cvonk/OPNpool_meets_ESPHome/components/opnpool/opnpoolstate_rx.cpp

/**
 * @brief OPNpool - Pool state: updates the state in response to network messages
 *
 * © Copyright 2014, 2019, 2022, 2026, Coert Vonk
 * 
 * This file is part of OPNpool.
 * OPNpool is free software: you can redistribute it and/or modify it under the terms of
 * the GNU General Public License as published by the Free Software Foundation, either
 * version 3 of the License, or (at your option) any later version.
 * OPNpool is distributed in the hope that it will be useful, but WITHOUT ANY WARRANTY;
 * without even the implied warranty of MERCHANTABILITY or FITNESS FOR A PARTICULAR PURPOSE.
 * See the GNU General Public License for more details.
 * You should have received a copy of the GNU General Public License along with OPNpool. 
 * If not, see <https://www.gnu.org/licenses/>.
 * 
 * SPDX-License-Identifier: GPL-3.0-or-later
 * SPDX-FileCopyrightText: Copyright 2014,2019,2022,2026 Coert Vonk
 */

#include <string.h>
#include <esp_system.h>
#include <freertos/FreeRTOS.h>
#include <freertos/task.h>
#include <freertos/semphr.h>
#include <esphome/core/log.h>
#include <cJSON.h>

#include "utils.h"
#include "network.h"
#include "network_msg.h"
#include "ipc.h"
#include "opnpoolstate.h"
#include "opnpool.h"

namespace esphome {
namespace opnpool {

static char const * const TAG = "opnpoolstate_rx";

/**
 * ctrl
 **/

void
OpnPoolState::rx_ctrl_time(cJSON * const dbg, network_msg_ctrl_time_t const * const msg, poolstate_t * const state)
{
    state->system.tod.time.minute = msg->minute;
    state->system.tod.time.hour = msg->hour;
    state->system.tod.date.day = msg->day;
    state->system.tod.date.month = msg->month;
    state->system.tod.date.year = (uint16_t)(2000) + msg->year;

    if (ESPHOME_LOG_LEVEL >= ESPHOME_LOG_LEVEL_VERBOSE) {
        opnpoolstate_log_add_tod(dbg, "tod", &state->system.tod);
    }
}

void
OpnPoolState::rx_ctrl_heat_resp(cJSON * const dbg, network_msg_ctrl_heat_resp_t const * const msg, poolstate_t * const state)
{
    uint8_t const pool_idx = static_cast<uint8_t>(poolstate_thermo_typ_t::POOL);
    uint8_t const spa_idx = static_cast<uint8_t>(poolstate_thermo_typ_t::SPA);

    state->thermos[pool_idx].temp = msg->poolTemp;
    state->thermos[pool_idx].set_point = msg->poolSetpoint;
    state->thermos[pool_idx].heat_src = msg->heatSrc & 0x03;
    state->thermos[spa_idx].temp = msg->spaTemp;
    state->thermos[spa_idx].set_point = msg->spaSetpoint;
    state->thermos[spa_idx].heat_src = (msg->heatSrc >> 2) & 0x03;

    if (ESPHOME_LOG_LEVEL >= ESPHOME_LOG_LEVEL_VERBOSE) {
        opnpoolstate_log_add_thermos(dbg, "thermos", state->thermos, true, true, true, false);
    }
}

void
OpnPoolState::rx_ctrl_heat_set(cJSON * const dbg, network_msg_ctrl_heat_set_t const * const msg, poolstate_t * const state)
{
    uint8_t const pool_idx = static_cast<uint8_t>(poolstate_thermo_typ_t::POOL);
    uint8_t const spa_idx = static_cast<uint8_t>(poolstate_thermo_typ_t::SPA);

    state->thermos[pool_idx].set_point = msg->poolSetpoint;
    state->thermos[pool_idx].heat_src = msg->heatSrc & 0x03;
    state->thermos[spa_idx].set_point = msg->spaSetpoint;
    state->thermos[spa_idx].heat_src = (msg->heatSrc >> 2) & 0x03;

    if (ESPHOME_LOG_LEVEL >= ESPHOME_LOG_LEVEL_VERBOSE) {
        opnpoolstate_log_add_thermos(dbg, "thermos", state->thermos, false, true, true, false);
    }
}

static void
_rx_ctrl_hex_bytes(cJSON * const dbg, uint8_t const * const bytes, poolstate_t * const state, uint8_t nrBytes)
{
    if (ESPHOME_LOG_LEVEL >= ESPHOME_LOG_LEVEL_VERBOSE) {
        cJSON * const array = cJSON_CreateArray();
        
        for (uint_least8_t ii = 0; ii < nrBytes; ii++) {
            char hex_str[3];  // "XX\0"
            ESP_LOGVV(TAG, "byte[%u] = 0x%02X", ii, bytes[ii]);
            snprintf(hex_str, sizeof(hex_str), "%02X", bytes[ii]);
            cJSON_AddItemToArray(array, cJSON_CreateString(hex_str));
        }
        cJSON_AddItemToObject(dbg, "raw", array);
    }
}

void
OpnPoolState::rx_ctrl_circuit_set(cJSON * const dbg, network_msg_ctrl_circuit_set_t const * const msg, poolstate_t * const state)
{
    state->circuits.active[msg->circuit -1] = msg->value;

    if (ESPHOME_LOG_LEVEL >= ESPHOME_LOG_LEVEL_VERBOSE) {
        {
            int idx = static_cast<int>(msg->circuit) - 1;
            if (idx >= 0) {
                cJSON_AddNumberToObject(dbg, network_pool_circuit_str(static_cast<network_pool_circuit_t>(idx)), msg->value);
            } else {
                cJSON_AddNumberToObject(dbg, "circuit_invalid", msg->value);
            }
        }
    }
}

void
OpnPoolState::rx_ctrl_sched_resp(cJSON * const dbg, network_msg_ctrl_sched_resp_t const * const msg, poolstate_t * const state)
{
    poolstate_sched_t * state_scheds = state->scheds;    
    memset(state_scheds, 0, sizeof(poolstate_sched_t) * NETWORK_MSG_CTRL_SCHED_COUNT );

    network_msg_ctrl_sched_resp_sub_t const * msg_sched = msg->scheds;

    for (uint8_t ii = 0; ii < NETWORK_MSG_CTRL_SCHED_COUNT; ii++, msg_sched++) {
        state_scheds[msg_sched->circuit -1] = (poolstate_sched_t) {
            .active = true,
            .start = static_cast<uint16_t>((static_cast<uint16_t>(msg_sched->prgStartHi) << 8) | static_cast<uint16_t>(msg_sched->prgStartLo)),
            .stop = static_cast<uint16_t>((static_cast<uint16_t>(msg_sched->prgStopHi) << 8) | static_cast<uint16_t>(msg_sched->prgStopLo))
        };
    }

    if (ESPHOME_LOG_LEVEL >= ESPHOME_LOG_LEVEL_VERBOSE) {
        opnpoolstate_log_add_sched(dbg, "scheds", state->scheds, true);
    }
}

void
OpnPoolState::rx_ctrl_state(cJSON * const dbg, network_msg_ctrl_state_bcast_t const * const msg, poolstate_t * state)
{
     // update state->circuits.active
    bool * state_active = state->circuits.active;
    uint16_t msg_mask = 0x00001;
    uint16_t const msg_active = ((uint16_t)msg->activeHi << 8) | msg->activeLo;
    for (uint8_t ii = 0; ii < NETWORK_POOL_MODE_COUNT; ii++, state_active++) {
        *state_active = msg_active & msg_mask;
        msg_mask <<= 1;
    }
        // if both SPA and POOL bits are set, only SPA runs
    if (state->circuits.active[static_cast<uint8_t>(network_pool_circuit_t::SPA)]) {
        state->circuits.active[static_cast<uint8_t>(network_pool_circuit_t::POOL)] = false;
    }

        // update state->circuits.delay
    bool * state_delay = state->circuits.delay;
    msg_mask = 0x00001;
    for (uint8_t ii = 0; ii < NETWORK_POOL_MODE_COUNT; ii++, state_delay++) {
        *state_delay = msg->delay & msg_mask;
        msg_mask <<= 1;
    }

        // update state->circuits.thermos (only update when the pump is running)
    uint8_t const pool_idx = static_cast<uint8_t>(poolstate_thermo_typ_t::POOL);
    uint8_t const spa_idx = static_cast<uint8_t>(poolstate_thermo_typ_t::SPA);

    if (state->circuits.active[static_cast<uint8_t>(network_pool_circuit_t::SPA)]) {
        state->thermos[spa_idx].temp = msg->poolTemp;
    }
    if (state->circuits.active[static_cast<uint8_t>(network_pool_circuit_t::POOL)]) {
        state->thermos[pool_idx].temp = msg->poolTemp;
    }
    state->thermos[pool_idx].heating = msg->heatStatus & 0x04;
    state->thermos[spa_idx].heating = msg->heatStatus & 0x08;
    state->thermos[pool_idx].heat_src = msg->heatSrc & 0x03;
    state->thermos[spa_idx].heat_src = (msg->heatSrc >> 2) & 0x03;

        // update state->modes.is_set
    bool * state_mode = state->modes.is_set;
    msg_mask = 0x00001;
    for (uint8_t ii = 0; ii < NETWORK_POOL_MODE_COUNT; ii++, state_mode++) {
        *state_mode = msg->modes & msg_mask;
        msg_mask <<= 1;
    }

        // update state->system (date is updated through `network_msg_ctrl_time`)
    state->system.tod.time.minute = msg->minute;
    state->system.tod.time.hour = msg->hour;

        // update state->temps
    uint8_t const air_idx = static_cast<uint8_t>(poolstate_temp_typ_t::AIR);
    uint8_t const water_idx = static_cast<uint8_t>(poolstate_temp_typ_t::WATER);

    state->temps[air_idx].temp = msg->airTemp;
    state->temps[water_idx].temp = msg->waterTemp;

    if (ESPHOME_LOG_LEVEL >= ESPHOME_LOG_LEVEL_VERBOSE) {
        opnpoolstate_log_add_state(dbg, "state", state);
    }
}

/**
 * version
 */

void
OpnPoolState::rx_ctrl_version_resp(cJSON * const dbg, network_msg_ctrl_version_resp_t const * const msg, poolstate_t * state)
{
    state->system.version.major = msg->major;
    state->system.version.minor = msg->minor;

    if (ESPHOME_LOG_LEVEL >= ESPHOME_LOG_LEVEL_VERBOSE) {
        opnpoolstate_log_add_version(dbg, "firmware", &state->system.version);
    }
}

/**
 * pump
 **/

void
OpnPoolState::rx_pump_reg_set(cJSON * const dbg, network_msg_pump_reg_set_t const * const msg)
{
    uint16_t const address = (msg->addressHi << 8) | msg->addressLo;
    uint16_t const value = (msg->valueHi << 8) | msg->valueLo;

    if (ESPHOME_LOG_LEVEL >= ESPHOME_LOG_LEVEL_VERBOSE) {
        opnpoolstate_log_add_pump_program(dbg, network_pump_program_str(address), value);
    }
}

void
OpnPoolState::rx_pump_reg_set_resp(cJSON * const dbg, network_msg_pump_reg_resp_t const * const msg)
{
    uint16_t const value = (msg->valueHi << 8) | msg->valueLo;

    if (ESPHOME_LOG_LEVEL >= ESPHOME_LOG_LEVEL_VERBOSE) {
        opnpoolstate_log_add_pump_program(dbg, "resp", value);
    }
}

void
OpnPoolState::rx_pump_ctrl(cJSON * const dbg, network_msg_pump_ctrl_t const * const msg)
{
    if (ESPHOME_LOG_LEVEL >= ESPHOME_LOG_LEVEL_VERBOSE) {
       opnpoolstate_log_add_pump_ctrl(dbg, "ctrl", msg->ctrl);
    }
}

void
OpnPoolState::rx_pump_mode(cJSON * const dbg, network_msg_pump_mode_t const * const msg, poolstate_t * const state)
{
    if (ESPHOME_LOG_LEVEL >= ESPHOME_LOG_LEVEL_VERBOSE) {
        opnpoolstate_log_add_pump_mode(dbg, "mode", msg->mode);
    }
    state->pump.mode = msg->mode;
}

void
OpnPoolState::rx_pump_run(cJSON * const dbg, network_msg_pump_run_t const * const msg, poolstate_t * const state)
{
    bool const running = msg->running == 0x0A;
    bool const not_running = msg->running == 0x04;
    if (!running && !not_running) {
        return;
    }
    state->pump.running = running;
    if (ESPHOME_LOG_LEVEL >= ESPHOME_LOG_LEVEL_VERBOSE) {
        opnpoolstate_log_add_pump_running(dbg, "running", state->pump.running);
    }
}

void
OpnPoolState::rx_pump_status(cJSON * const dbg, network_msg_pump_status_resp_t const * const msg, poolstate_t * const state)
{
    bool const running = msg->running == 0x0A;
    bool const not_running = msg->running == 0x04;
    if (!running && !not_running) {
        return;
    }
    state->pump.running = running;
    state->pump.mode = msg->mode;
    state->pump.state = msg->state;
    state->pump.power = ((uint16_t)msg->powerHi << 8) | msg->powerLo;
    state->pump.speed = ((uint16_t)msg->speedHi << 8) | msg->speedLo;
    state->pump.flow = msg->flow;
    state->pump.level = msg->level;
    state->pump.error = msg->error;
    state->pump.timer = msg->remainingMin;
    state->pump.time.hour = msg->clockHr;
    state->pump.time.minute = msg->clockMin;

    if (ESPHOME_LOG_LEVEL >= ESPHOME_LOG_LEVEL_VERBOSE) {
       opnpoolstate_log_add_pump(dbg, "status", state);
    }
}

void
OpnPoolState::rx_ctrl_set_ack(cJSON * const dbg, network_msg_ctrl_set_ack_t const * const msg)
{
    if (ESPHOME_LOG_LEVEL >= ESPHOME_LOG_LEVEL_VERBOSE) {
        cJSON_AddNumberToObject(dbg, "ack", msg->typ);
    }
}

/**
 * chlor
 **/

void
OpnPoolState::rx_chlor_name_resp(cJSON * const dbg, network_msg_chlor_name_resp_t const * const msg, poolstate_t * const state)
{
    state->chlor.salt = (uint16_t)msg->salt * 50;

    size_t name_size = sizeof(state->chlor.name);
    strncpy(state->chlor.name, msg->name, name_size);
    state->chlor.name[name_size - 1] = '\0';

    if (ESPHOME_LOG_LEVEL >= ESPHOME_LOG_LEVEL_VERBOSE) {
        cJSON_AddNumberToObject(dbg, "salt", state->chlor.salt);
        cJSON_AddStringToObject(dbg, "name", state->chlor.name);
    }
}

void
OpnPoolState::rx_chlor_level_set(cJSON * const dbg, network_msg_chlor_level_set_t const * const msg, poolstate_t * const state)
{
    state->chlor.level = msg->level;

    if (ESPHOME_LOG_LEVEL >= ESPHOME_LOG_LEVEL_VERBOSE) {
        cJSON_AddNumberToObject(dbg, "level", state->chlor.level);
    }
}

void
OpnPoolState::rx_chlor_level_set_resp(cJSON * const dbg, network_msg_chlor_level_resp_t const * const msg, poolstate_t * const state)
{
    state->chlor.salt = (uint16_t)msg->salt * 50;
    if (msg->error & 0x01) {
        state->chlor.status = poolstate_chlor_status_t::LOW_FLOW;
    } else if (msg->error & 0x02) {
        state->chlor.status = poolstate_chlor_status_t::LOW_SALT;
    } else if (msg->error & 0x04) {
        state->chlor.status = poolstate_chlor_status_t::HIGH_SALT;
    } else if (msg->error & 0x10) {
        state->chlor.status = poolstate_chlor_status_t::CLEAN_CELL;
    } else if (msg->error & 0x40) {
        state->chlor.status = poolstate_chlor_status_t::COLD;
    } else if (msg->error & 0x80) {
        state->chlor.status = poolstate_chlor_status_t::OK;
    } else {
        state->chlor.status = poolstate_chlor_status_t::OTHER;
    }
    // good salt range is 2600 to 4500 ppm

    if (ESPHOME_LOG_LEVEL >= ESPHOME_LOG_LEVEL_VERBOSE) {
        opnpoolstate_log_add_chlor_resp(dbg, "chlor", &state->chlor);
    }
}

esp_err_t
OpnPoolState::rx_update(network_msg_t const * const msg)
{
  	name_reset_idx();

        // remember the current state
    poolstate_t old_state;
    (void) get(&old_state);

        // start with the current state
    poolstate_t new_state;
    memcpy(&new_state, &old_state, sizeof(poolstate_t));

        // adjust the new_state based on the incoming message
    cJSON * const dbg = cJSON_CreateObject();
    switch (msg->typ) {
        case network_msg_typ_t::CTRL_SET_ACK:  // response to various set requests
            rx_ctrl_set_ack(dbg, &msg->u.ctrl_set_ack);
            break;
        case network_msg_typ_t::CTRL_CIRCUIT_SET:
            rx_ctrl_circuit_set(dbg, &msg->u.ctrl_circuit_set, &new_state);
            break;
        case network_msg_typ_t::CTRL_SCHED_REQ:
            break;
        case network_msg_typ_t::CTRL_SCHED_RESP:
            rx_ctrl_sched_resp(dbg, &msg->u.ctrl_sched_resp, &new_state);
            break;
        case network_msg_typ_t::CTRL_STATE_BCAST:
            rx_ctrl_state(dbg, &msg->u.ctrl_state, &new_state);
            break;
        case network_msg_typ_t::CTRL_TIME_REQ:
            break;
        case network_msg_typ_t::CTRL_TIME_RESP:
            rx_ctrl_time(dbg, &msg->u.ctrl_time_resp, &new_state);
            break;
        case network_msg_typ_t::CTRL_TIME_SET:
            rx_ctrl_time(dbg, &msg->u.ctrl_time_set, &new_state);
            break;
        case network_msg_typ_t::CTRL_HEAT_REQ:
            break;
        case network_msg_typ_t::CTRL_HEAT_RESP:
            rx_ctrl_heat_resp(dbg, &msg->u.ctrl_heat_resp, &new_state);
            break;
        case network_msg_typ_t::CTRL_HEAT_SET:
            rx_ctrl_heat_set(dbg, &msg->u.ctrl_heat_set, &new_state);
            break;
        case network_msg_typ_t::CTRL_LAYOUT_REQ:
        case network_msg_typ_t::CTRL_LAYOUT_RESP:
        case network_msg_typ_t::CTRL_LAYOUT_SET:
        case network_msg_typ_t::CTRL_VALVE_REQ:
        case network_msg_typ_t::CTRL_SOLARPUMP_REQ:
        case network_msg_typ_t::CTRL_DELAY_REQ:
        case network_msg_typ_t::CTRL_HEAT_SETPT_REQ:
        case network_msg_typ_t::CTRL_VERSION_REQ:
            break;
        case network_msg_typ_t::CTRL_SCHEDS_REQ:
        case network_msg_typ_t::CTRL_CIRC_NAMES_REQ:
        case network_msg_typ_t::CTRL_CHEM_REQ:
        case network_msg_typ_t::CHLOR_NAME_REQ:
            _rx_ctrl_hex_bytes(dbg, msg->u.bytes, &new_state, 1);
            break;
        case network_msg_typ_t::CTRL_VERSION_RESP:
            rx_ctrl_version_resp(dbg, &msg->u.ctrl_version_resp, &new_state);
            break;
        case network_msg_typ_t::CTRL_VALVE_RESP:
            _rx_ctrl_hex_bytes(dbg, msg->u.bytes, &new_state, sizeof(network_msg_ctrl_valve_resp_t));
            break;
        case network_msg_typ_t::CTRL_SOLARPUMP_RESP:
            _rx_ctrl_hex_bytes(dbg, msg->u.bytes, &new_state, sizeof(network_msg_ctrl_solarpump_resp_t));
            break;
        case network_msg_typ_t::CTRL_DELAY_RESP:
            _rx_ctrl_hex_bytes(dbg, msg->u.bytes, &new_state, sizeof(network_msg_ctrl_delay_resp_t));
            break;
        case network_msg_typ_t::CTRL_HEAT_SETPT_RESP:
            _rx_ctrl_hex_bytes(dbg, msg->u.bytes, &new_state, sizeof(network_msg_ctrl_heat_setpt_resp_t));
            break;
        case network_msg_typ_t::CTRL_CIRC_NAMES_RESP:
            _rx_ctrl_hex_bytes(dbg, msg->u.bytes, &new_state, sizeof(network_msg_ctrl_circ_names_resp_t));
            break;
        case network_msg_typ_t::CTRL_SCHEDS_RESP:
            _rx_ctrl_hex_bytes(dbg, msg->u.bytes, &new_state, sizeof(network_msg_ctrl_scheds_resp_t));
            break;
        case network_msg_typ_t::PUMP_REG_SET:
            rx_pump_reg_set(dbg, &msg->u.pump_reg_set);
            break;
        case network_msg_typ_t::PUMP_REG_RESP:
            rx_pump_reg_set_resp(dbg, &msg->u.pump_reg_set_resp);
            break;
        case network_msg_typ_t::PUMP_CTRL_SET:
        case network_msg_typ_t::PUMP_CTRL_RESP:
            rx_pump_ctrl(dbg, &msg->u.pump_ctrl);
            break;
        case network_msg_typ_t::PUMP_MODE_SET:
        case network_msg_typ_t::PUMP_MODE_RESP:
            rx_pump_mode(dbg, &msg->u.pump_mode, &new_state);
            break;
        case network_msg_typ_t::PUMP_RUN_SET:
        case network_msg_typ_t::PUMP_RUN_RESP:
            rx_pump_run(dbg, &msg->u.pump_run, &new_state);
            break;
        case network_msg_typ_t::PUMP_STATUS_REQ:
             break;
        case network_msg_typ_t::PUMP_STATUS_RESP:
            rx_pump_status(dbg, &msg->u.pump_status_resp, &new_state);
            break;
        case network_msg_typ_t::CHLOR_PING_REQ:
        case network_msg_typ_t::CHLOR_PING_RESP:
            break;
        case network_msg_typ_t::CHLOR_NAME_RESP:
            rx_chlor_name_resp(dbg, &msg->u.chlor_name_resp, &new_state);
            break;
        case network_msg_typ_t::CHLOR_LEVEL_SET:
            rx_chlor_level_set(dbg, &msg->u.chlor_level_set, &new_state);
            break;
        case network_msg_typ_t::CHLOR_LEVEL_RESP:
            rx_chlor_level_set_resp(dbg, &msg->u.chlor_level_resp, &new_state);
            break;
    }

    bool const frequent = msg->typ == network_msg_typ_t::CTRL_STATE_BCAST ||
                          msg->typ == network_msg_typ_t::CHLOR_LEVEL_SET ||
                          msg->typ == network_msg_typ_t::PUMP_CTRL_SET ||
                          msg->typ == network_msg_typ_t::PUMP_CTRL_RESP ||
                          msg->typ == network_msg_typ_t::PUMP_RUN_SET ||
                          msg->typ == network_msg_typ_t::PUMP_RUN_RESP ||
                          msg->typ == network_msg_typ_t::PUMP_STATUS_REQ ||
                          msg->typ == network_msg_typ_t::PUMP_STATUS_RESP;
    bool const verbose = ESPHOME_LOG_LEVEL >= ESPHOME_LOG_LEVEL_VERBOSE;
    bool const very_verbose = ESPHOME_LOG_LEVEL >= ESPHOME_LOG_LEVEL_VERY_VERBOSE;

    if ((verbose && !frequent) || very_verbose) {
        size_t const json_size = 1024;
        char * const json = static_cast<char *>(calloc(1, json_size));
        assert(json);
        assert(cJSON_PrintPreallocated(dbg, json, json_size, false));
        ESP_LOGV(TAG, "{%s: %s}\n", network_msg_typ_str(msg->typ), json);
        free(json);
    }
    cJSON_Delete(dbg);

    bool const state_changed = memcmp(&new_state, &old_state, sizeof(poolstate_t)) != 0;

    ESP_LOGVV(TAG, "State comparison: AUX2(%u) old_state=%u new_state=%u => state_changed=%u", 
        static_cast<uint8_t>(network_pool_circuit_t::AUX2),
        old_state.circuits.active[static_cast<uint8_t>(network_pool_circuit_t::AUX2)],
        new_state.circuits.active[static_cast<uint8_t>(network_pool_circuit_t::AUX2)],
        state_changed);

    if (state_changed) {
        set(&new_state);
        
        // update state in HA
        parent_->update_all(&new_state);
    }
    return state_changed ? ESP_OK : ESP_FAIL;
}

} // namespace opnpool
} // namespace esphome  
